lata-mas/DH2O/Imagenes/BaseCarcasa.PNG

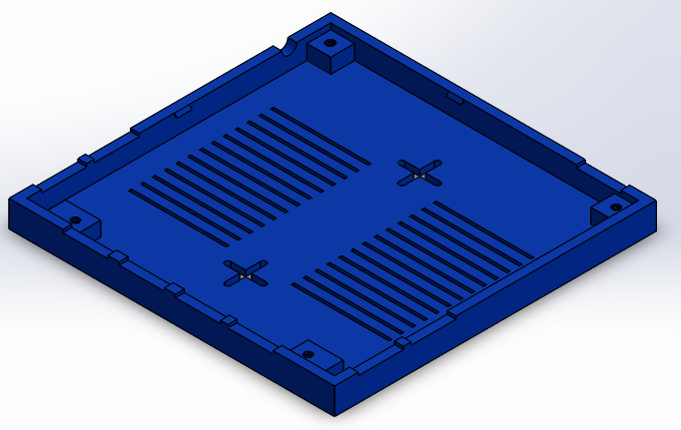
Imagenes/BaseCarcasa.PNG
