lata-mas/DH2O/Imagenes/BaseDeCarcasaPCB.PNG

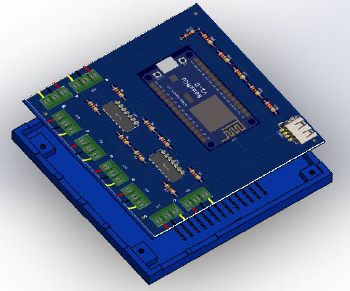
Imagenes/BaseDeCarcasaPCB.PNG
