lata-mas/DH2O/Imagenes/BaseDeCarcasaTornillos.PNG

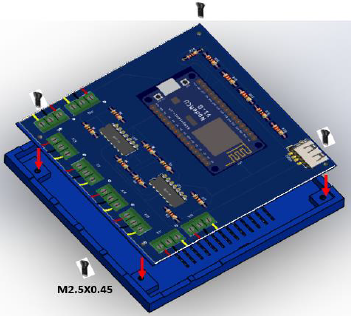
Imagenes/BaseDeCarcasaTornillos.PNG
