lata-mas/DH2O/Imagenes/BaseMediaCarcasa.PNG

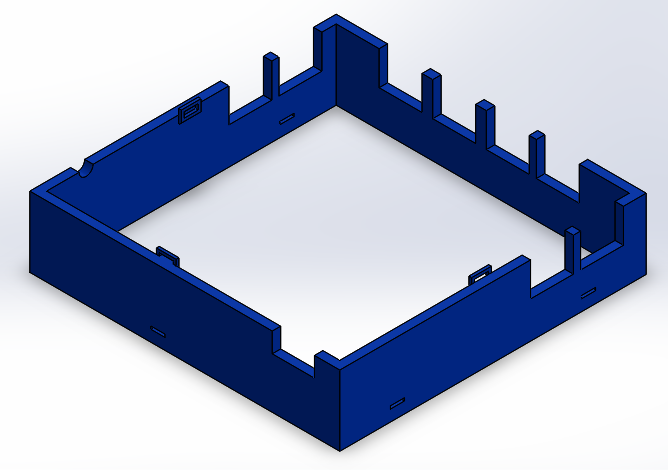
Imagenes/BaseMediaCarcasa.PNG
