lata-mas/DH2O/Imagenes/BASEYPLACA1.PNG

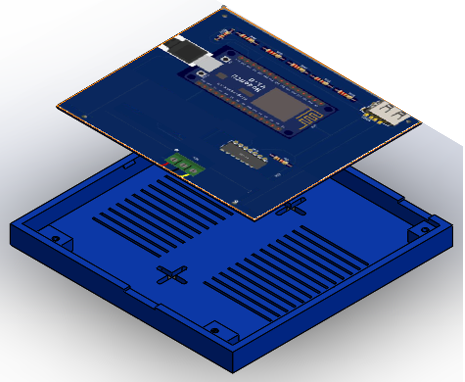
Imagenes/BASEYPLACA1.PNG
