lata-mas/DH2O/Imagenes/BASEYPLACA.PNG

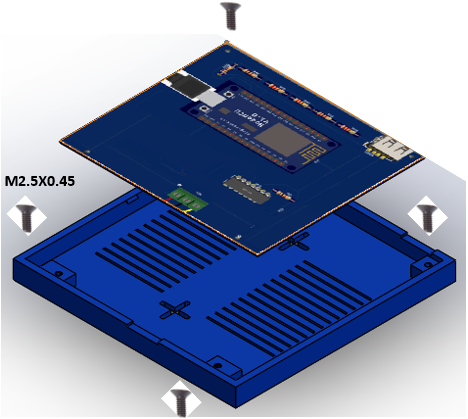
Imagenes/BASEYPLACA.PNG
