lata-mas/DH2O/Imagenes/CarateristicasNodeMCU.PNG

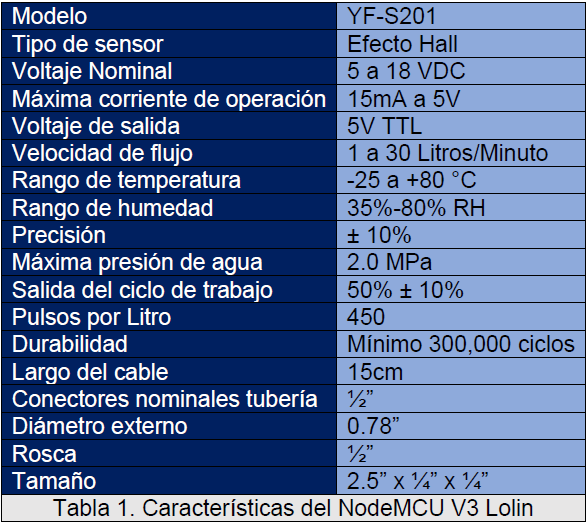
Imagenes/CarateristicasNodeMCU.PNG
