lata-mas/DH2O/Imagenes/CarateristicasNodeMCUB.PNG

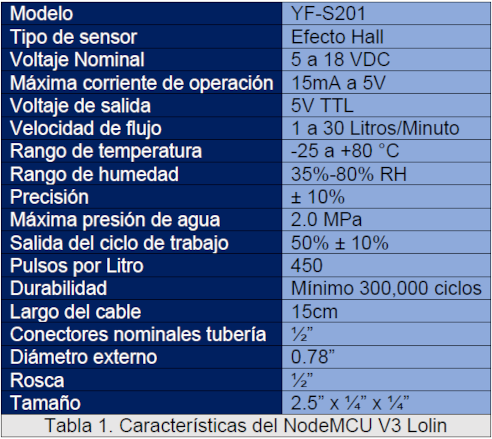
Imagenes/CarateristicasNodeMCUB.PNG
