lata-mas/DH2O/Imagenes/CarcasaH2O.PNG

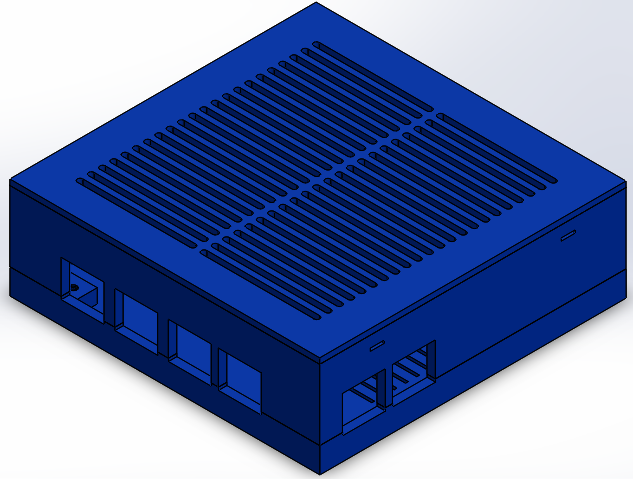
Imagenes/CarcasaH2O.PNG
