lata-mas/DH2O/Imagenes/Codigo5.PNG

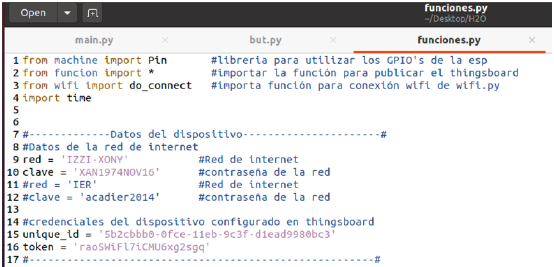
Imagenes/Codigo5.PNG
