lata-mas/DH2O/Imagenes/Codigo5B.PNG

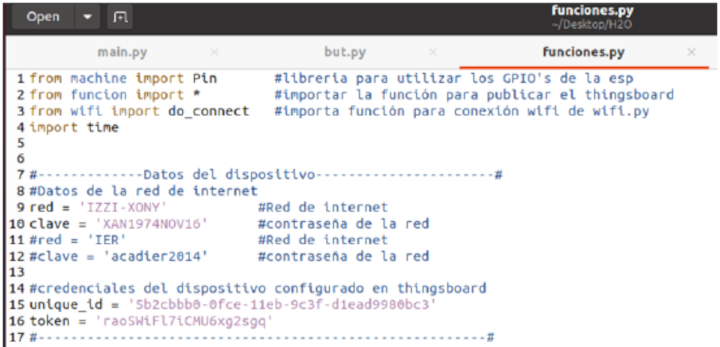
Imagenes/Codigo5B.PNG
