lata-mas/DH2O/Imagenes/COMPONENTESENPLACACOMPLETA.PNG

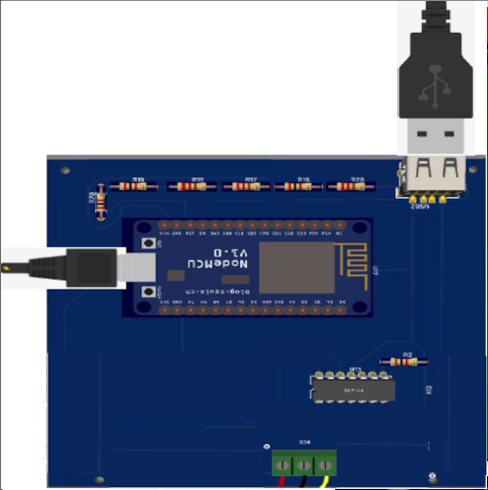
Imagenes/COMPONENTESENPLACACOMPLETA.PNG
