lata-mas/DH2O/Imagenes/Conexión de 2 sensores H2O.PNG

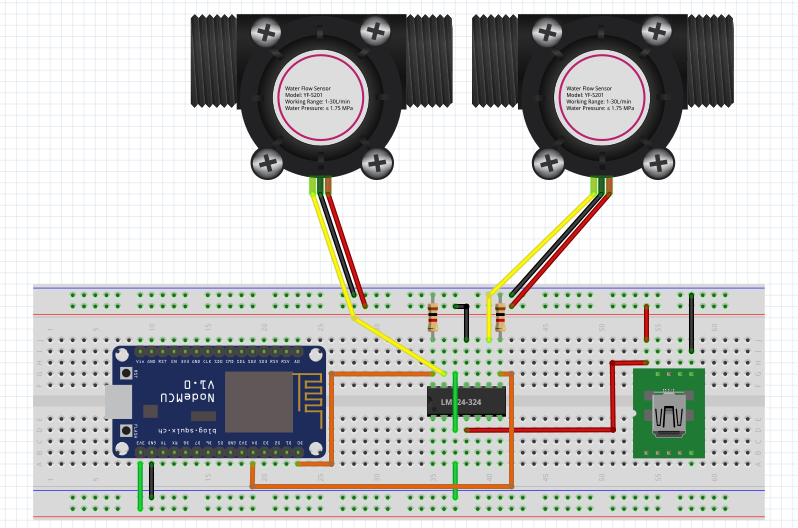
Imagenes/Conexión de 2 sensores H2O.PNG
