lata-mas/DH2O/Imagenes/Conexión_1S.PNG

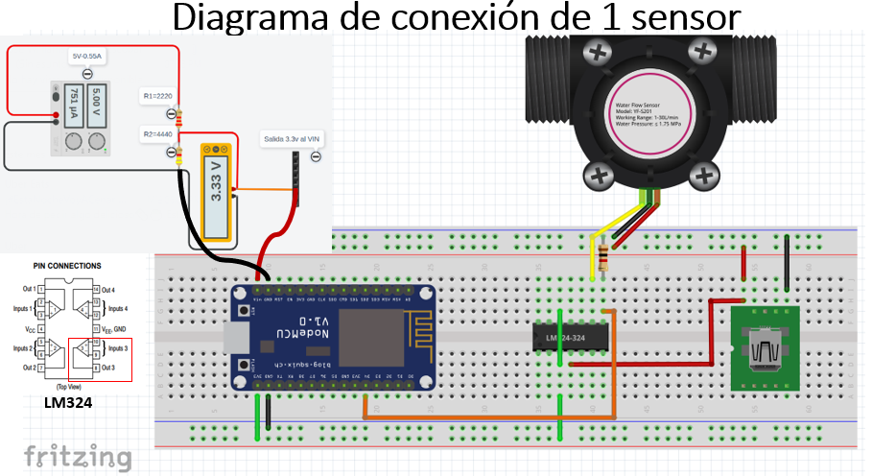
Imagenes/Conexión_1S.PNG
