lata-mas/DH2O/Imagenes/Conexión_8S H2O.PNG

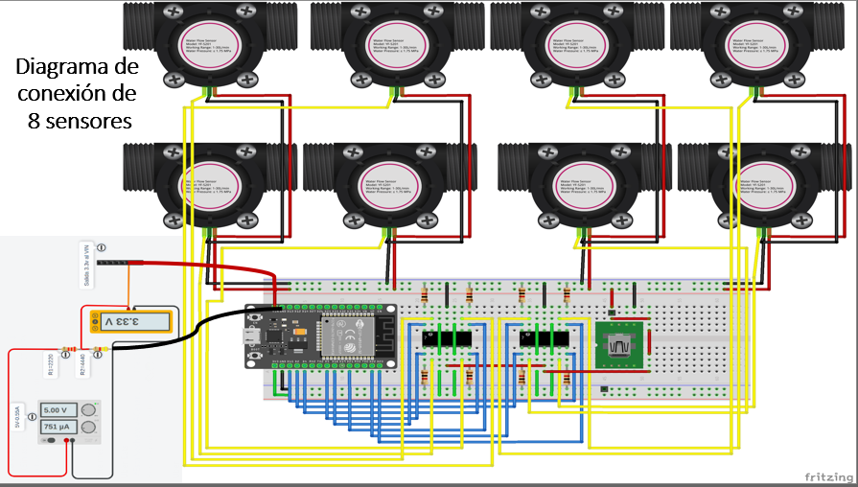
Imagenes/Conexión_8S H2O.PNG
