lata-mas/DH2O/Imagenes/CORRECTOINCORRECTO.PNG

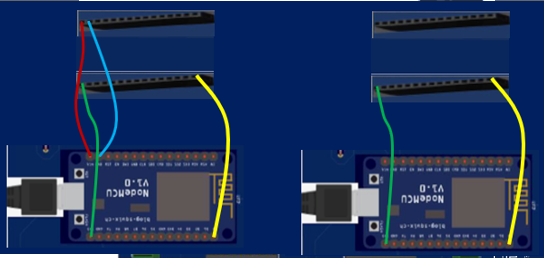
Imagenes/CORRECTOINCORRECTO.PNG
