lata-mas/DH2O/Imagenes/DetallesNodeMCU.PNG

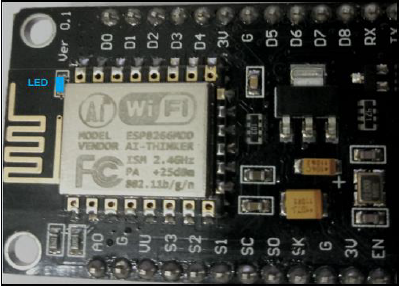
Imagenes/DetallesNodeMCU.PNG
