lata-mas/DH2O/Imagenes/DILLINGERB.png

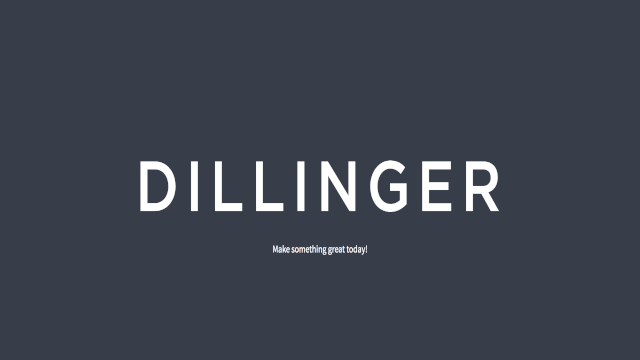
Imagenes/DILLINGERB.png
