lata-mas/DH2O/Imagenes/DimensionesPCBH2O.PNG

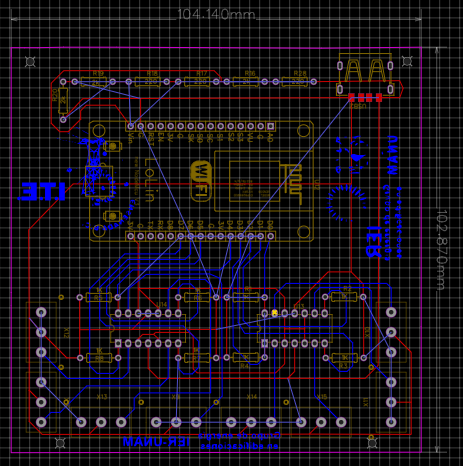
Imagenes/DimensionesPCBH2O.PNG
