lata-mas/DH2O/Imagenes/Divisor de V para el ESP-H2O.png

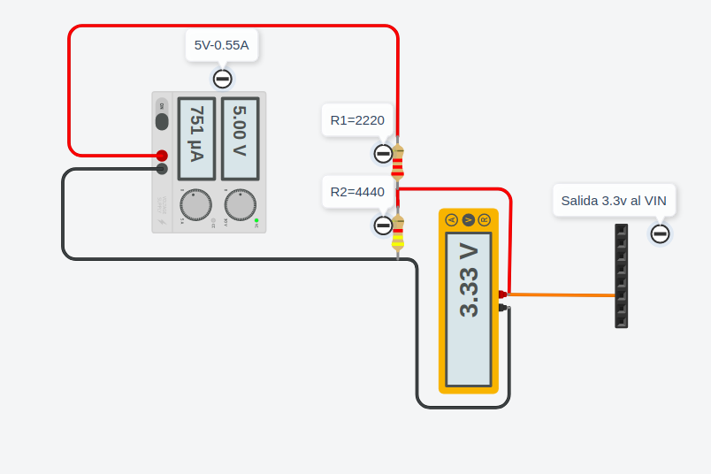
Imagenes/Divisor de V para el ESP-H2O.png
