lata-mas/DH2O/Imagenes/ErroresSolucion.PNG

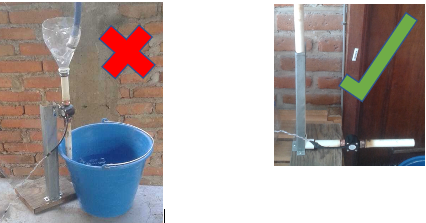
Imagenes/ErroresSolucion.PNG
