lata-mas/DH2O/Imagenes/ErroresSoluciones1.png

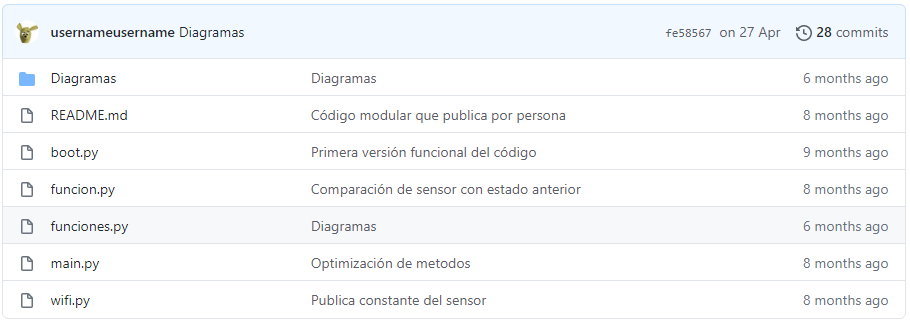
Imagenes/ErroresSoluciones1.png
