lata-mas/DH2O/Imagenes/ErroresSoluciones2.png

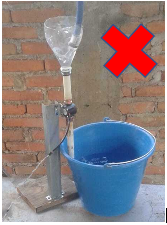
Imagenes/ErroresSoluciones2.png
