lata-mas/DH2O/Imagenes/ErroresSoluciones3.png

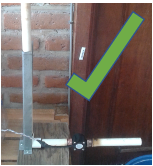
Imagenes/ErroresSoluciones3.png
