lata-mas/DH2O/Imagenes/ESPENPLACA.PNG

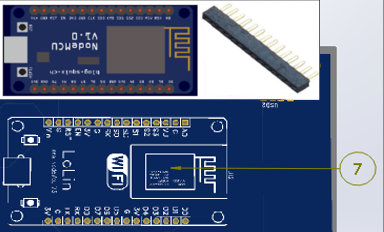
Imagenes/ESPENPLACA.PNG
