lata-mas/DH2O/Imagenes/FormaCorrectaIncorrecta.PNG

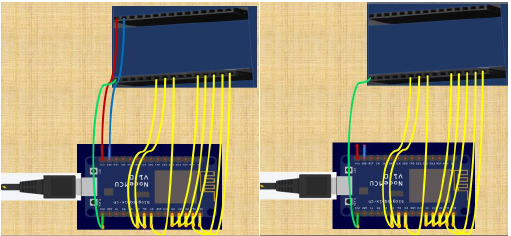
Imagenes/FormaCorrectaIncorrecta.PNG
