lata-mas/DH2O/Imagenes/IDENTIFICACIONCOMPH2O1.PNG

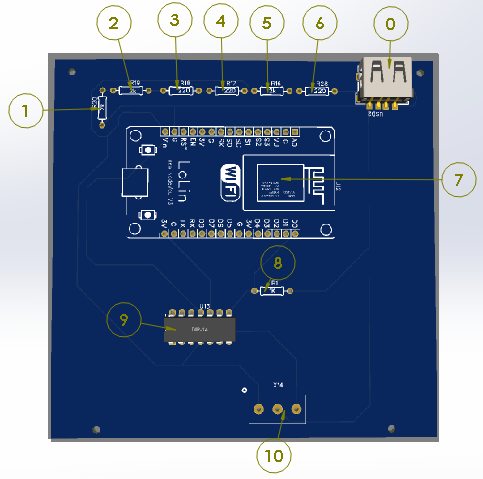
Imagenes/IDENTIFICACIONCOMPH2O1.PNG
