lata-mas/DH2O/Imagenes/IdentificacionDePatillaje.PNG

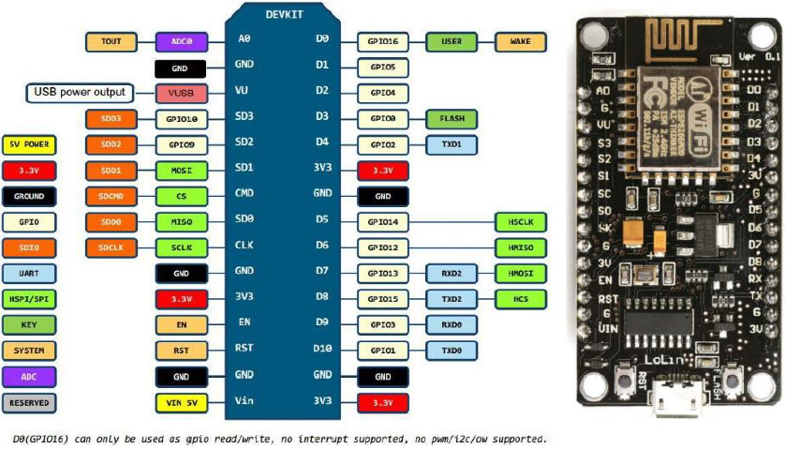
Imagenes/IdentificacionDePatillaje.PNG
