lata-mas/DH2O/Imagenes/ImagenCorteDePines.PNG

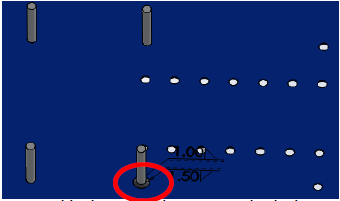
Imagenes/ImagenCorteDePines.PNG
