lata-mas/DH2O/Imagenes/ImagenESPEnPlaca.PNG

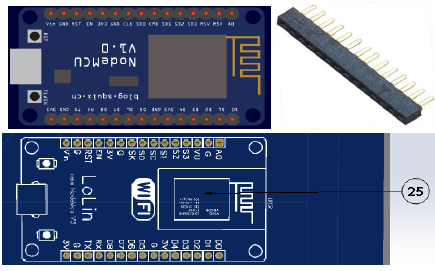
Imagenes/ImagenESPEnPlaca.PNG
