lata-mas/DH2O/Imagenes/LedESP.PNG

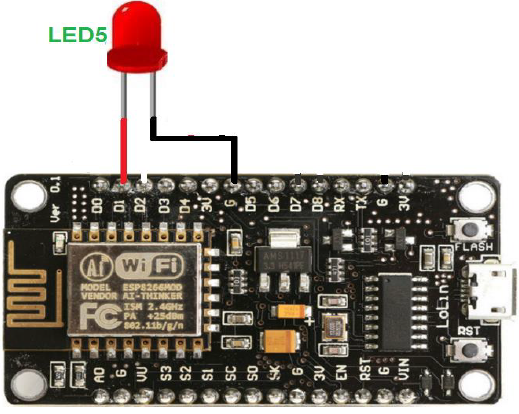
Imagenes/LedESP.PNG
