lata-mas/DH2O/Imagenes/LedsAzules.PNG

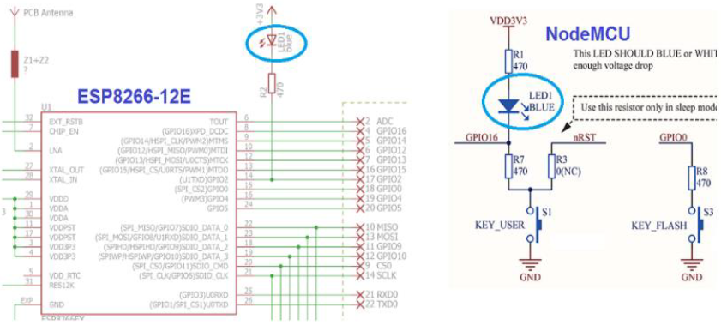
Imagenes/LedsAzules.PNG
