lata-mas/DH2O/Imagenes/ListarEnLinux.PNG

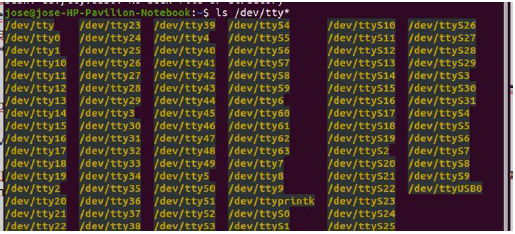
Imagenes/ListarEnLinux.PNG
