lata-mas/DH2O/Imagenes/M_Editor.PNG

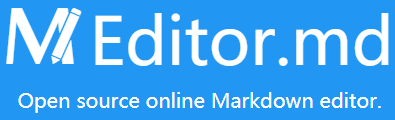
Imagenes/M_Editor.PNG
