lata-mas/DH2O/Imagenes/OpenKnow-How.PNG

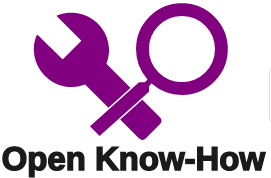
Imagenes/OpenKnow-How.PNG
