lata-mas/DH2O/Imagenes/OrientacionLM324.PNG

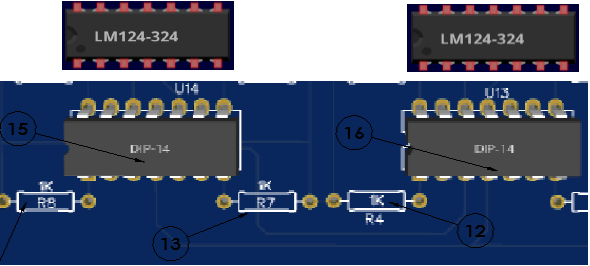
Imagenes/OrientacionLM324.PNG
