lata-mas/DH2O/Imagenes/Partes EsambleCompleto.PNG

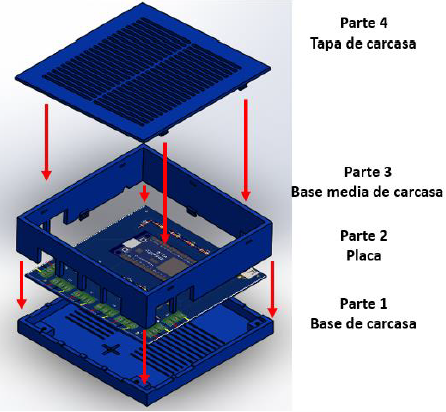
Imagenes/Partes EsambleCompleto.PNG
