lata-mas/DH2O/Imagenes/PatillajeESP.PNG

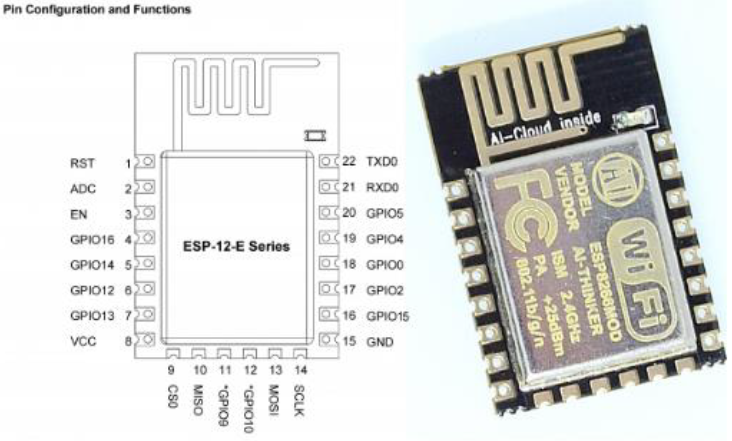
Imagenes/PatillajeESP.PNG
