lata-mas/DH2O/Imagenes/PCB3DEASYH2O1FRONTAL.PNG

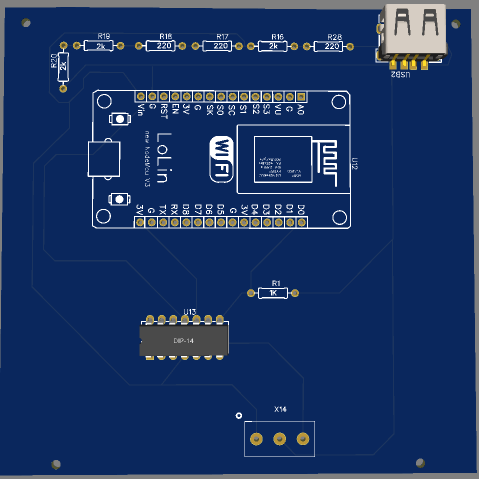
Imagenes/PCB3DEASYH2O1FRONTAL.PNG
