lata-mas/DH2O/Imagenes/PCB_H2O PCB.png

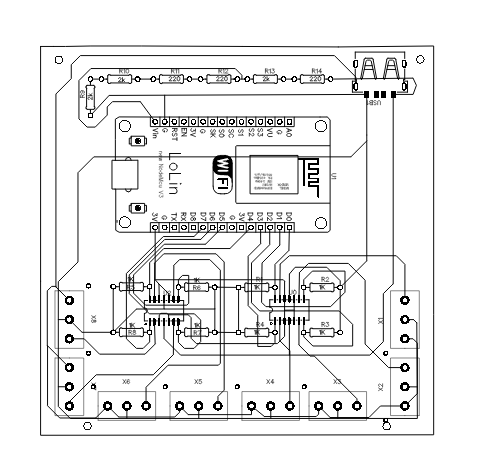
Imagenes/PCB_H2O PCB.png
