lata-mas/DH2O/Imagenes/PCBEASYH2O13DABAJO.PNG

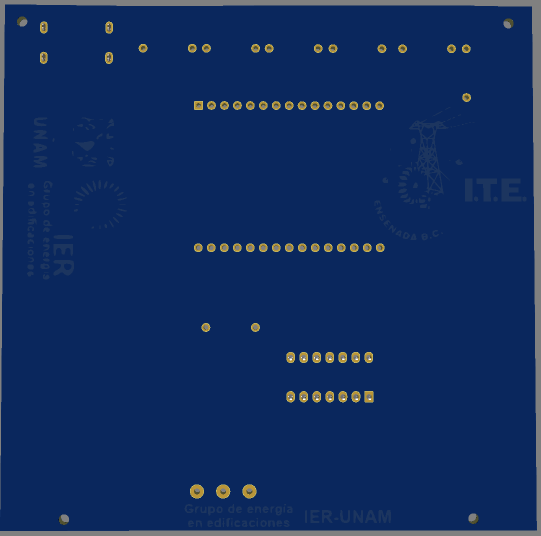
Imagenes/PCBEASYH2O13DABAJO.PNG
