lata-mas/DH2O/Imagenes/PinesCortados.PNG

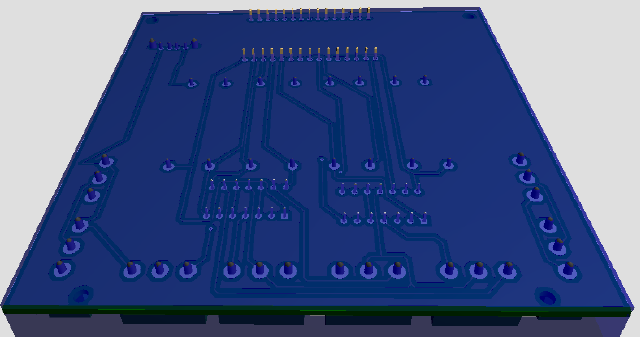
Imagenes/PinesCortados.PNG
