lata-mas/DH2O/Imagenes/PinesCortadosB.PNG

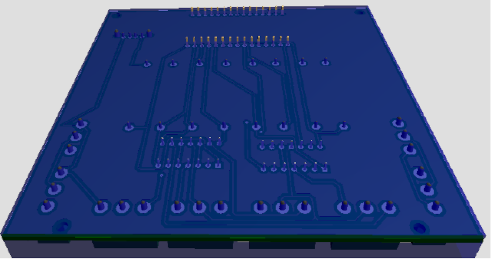
Imagenes/PinesCortadosB.PNG
