lata-mas/DH2O/Imagenes/PINESCUTPLACA1.PNG

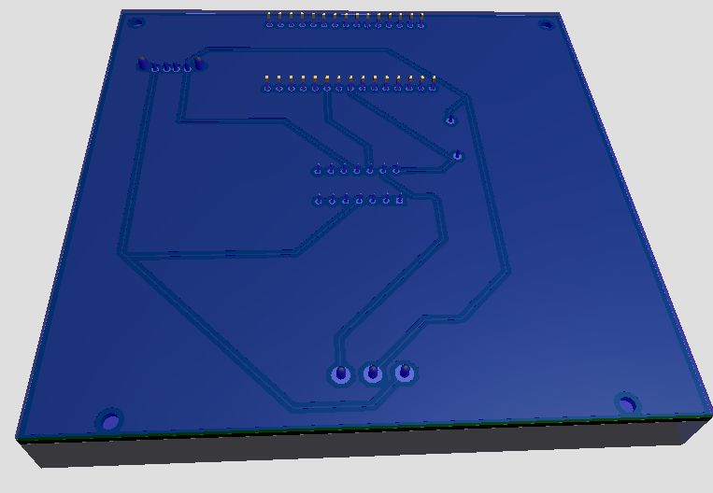
Imagenes/PINESCUTPLACA1.PNG
