lata-mas/DH2O/Imagenes/PINESCUTPLACA.PNG

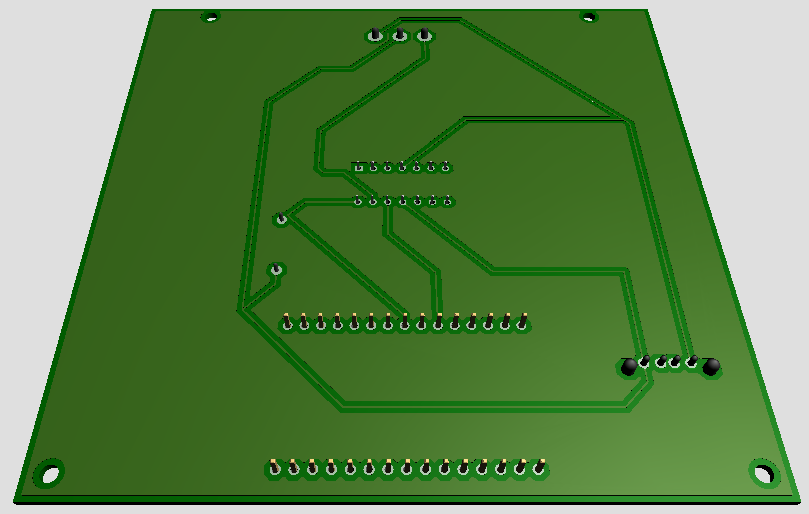
Imagenes/PINESCUTPLACA.PNG
