lata-mas/DH2O/Imagenes/PlacaWithComponetes.PNG

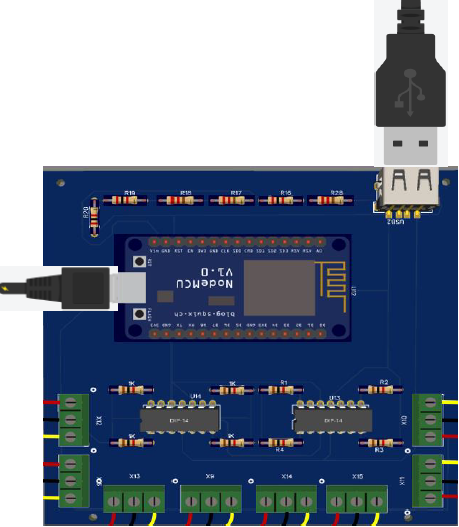
Imagenes/PlacaWithComponetes.PNG
