lata-mas/DH2O/Imagenes/PORTADAH2O1.PNG

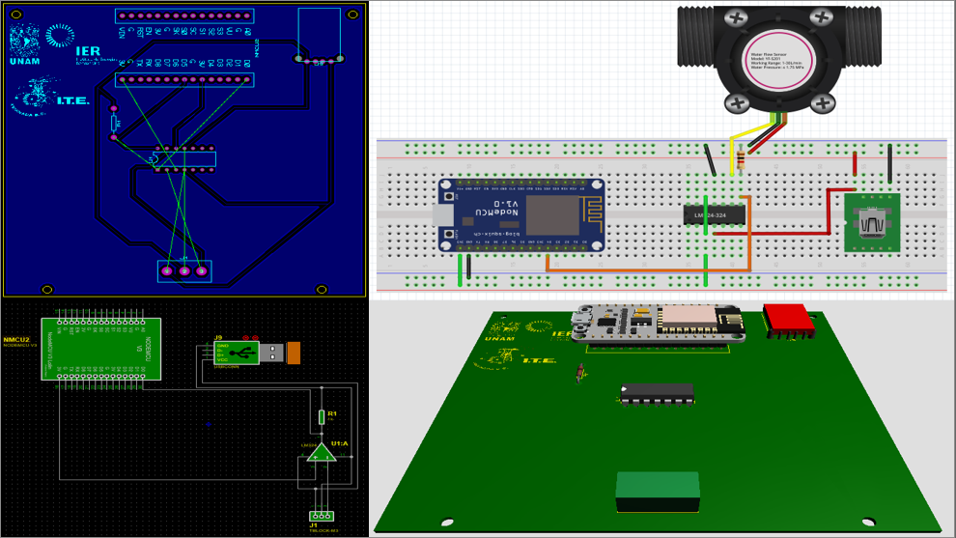
Imagenes/PORTADAH2O1.PNG
