lata-mas/DH2O/Imagenes/RelacionDeTerminales.PNG

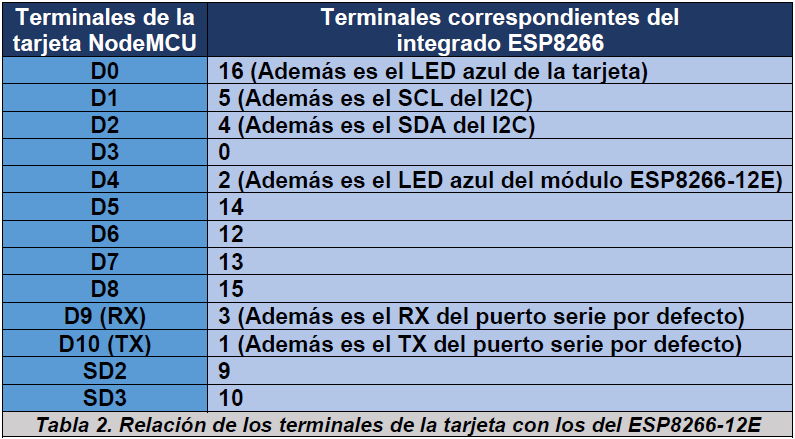
Imagenes/RelacionDeTerminales.PNG
