lata-mas/DH2O/Imagenes/ResistenciasDeParteSuperior.PNG

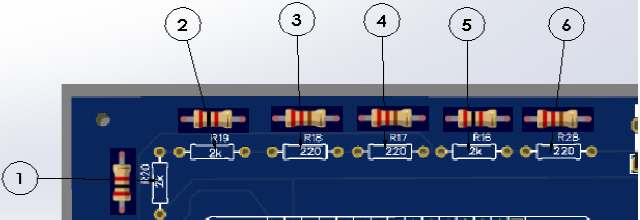
Imagenes/ResistenciasDeParteSuperior.PNG
