lata-mas/DH2O/Imagenes/ResistenciasDeParteSuperiorB.PNG

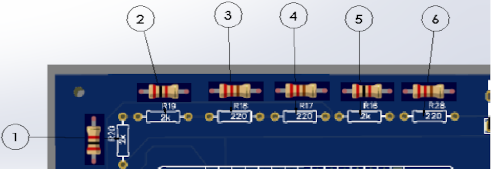
Imagenes/ResistenciasDeParteSuperiorB.PNG
