lata-mas/DH2O/Imagenes/ResistenciasParteInferior.PNG

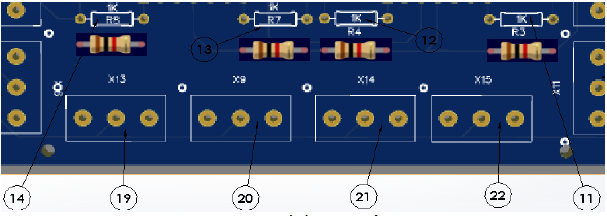
Imagenes/ResistenciasParteInferior.PNG
