lata-mas/DH2O/Imagenes/SENSORCONECTADO.PNG

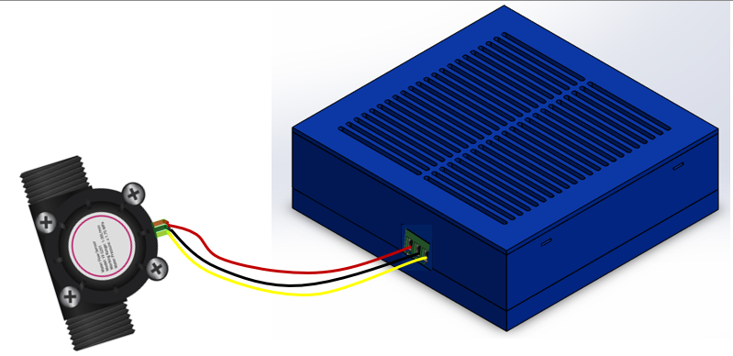
Imagenes/SENSORCONECTADO.PNG
