lata-mas/DH2O/Imagenes/SENSORENPLACA.PNG

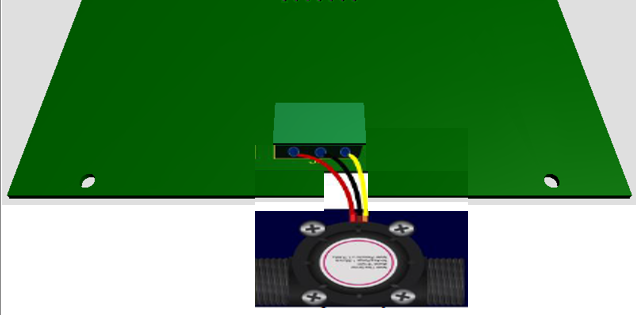
Imagenes/SENSORENPLACA.PNG
