lata-mas/DH2O/Imagenes/SensoresDerechos.PNG

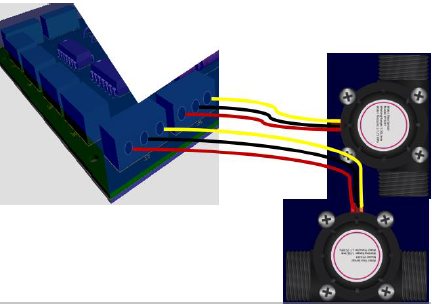
Imagenes/SensoresDerechos.PNG
