lata-mas/DH2O/Imagenes/SensoresFrontales.PNG

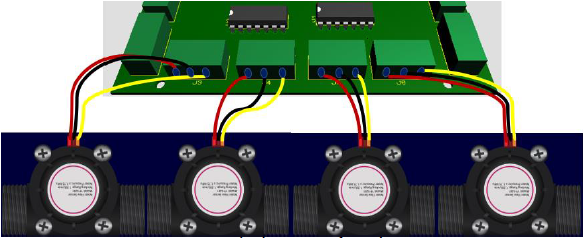
Imagenes/SensoresFrontales.PNG
