lata-mas/DH2O/Imagenes/SensoresIzquierdos.PNG

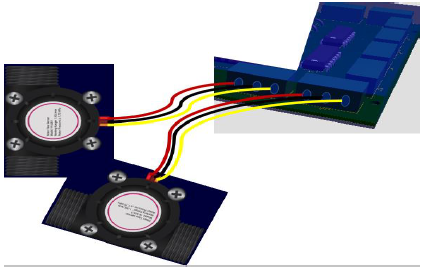
Imagenes/SensoresIzquierdos.PNG
