lata-mas/DH2O/Imagenes/TapaCarcasa.PNG

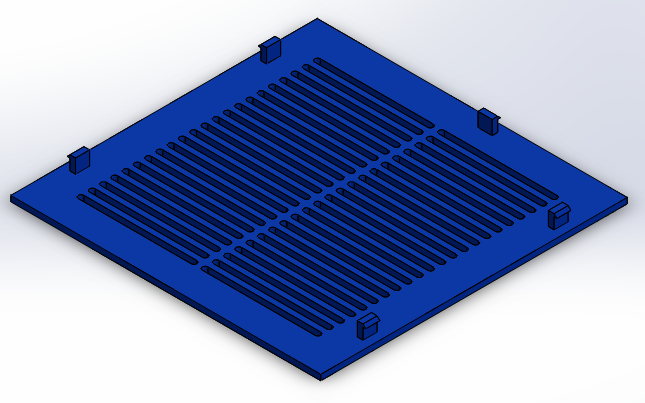
Imagenes/TapaCarcasa.PNG
