lata-mas/DH2O/Imagenes/TBLOCK-M3.PNG

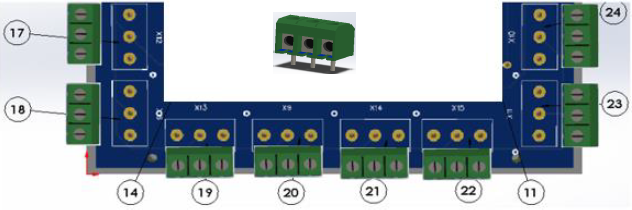
Imagenes/TBLOCK-M3.PNG
