lata-mas/DH2O/Imagenes/TBLOCKENPLACA.PNG

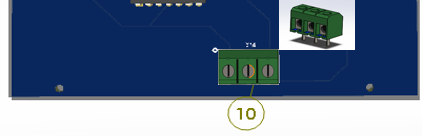
Imagenes/TBLOCKENPLACA.PNG
