lata-mas/DH2O/Imagenes/Thingsboard1.PNG

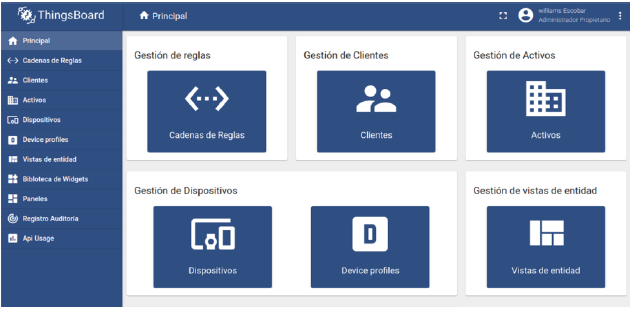
Imagenes/Thingsboard1.PNG
