lata-mas/DH2O/Imagenes/Thingsboard3.PNG

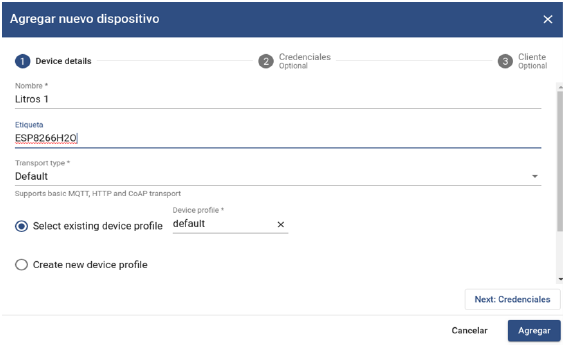
Imagenes/Thingsboard3.PNG
