lata-mas/DH2O/Imagenes/Thingsboard4.PNG

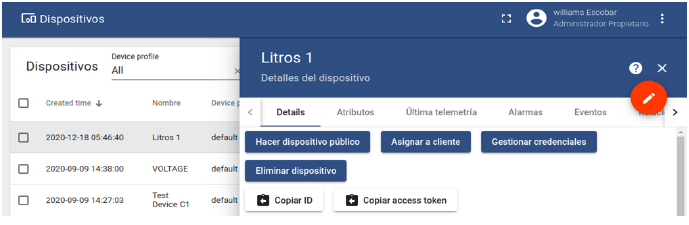
Imagenes/Thingsboard4.PNG
