lata-mas/DH2O/Imagenes/Thingsboard6.PNG

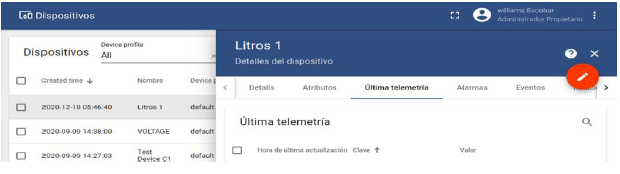
Imagenes/Thingsboard6.PNG
