lata-mas/DH2O/Imagenes/Thingsboard6B.PNG

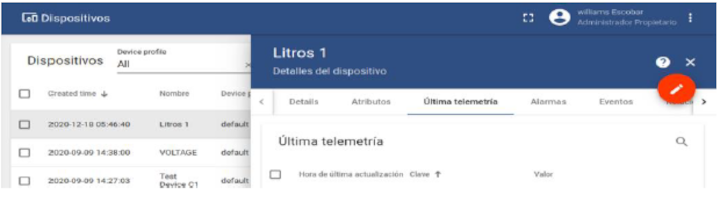
Imagenes/Thingsboard6B.PNG
