lata-mas/DH2O/Imagenes/USBCONN.PNG

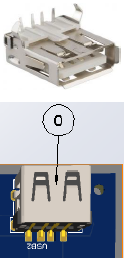
Imagenes/USBCONN.PNG
