lata-mas/DH2O/Imagenes/VersionesESP.PNG

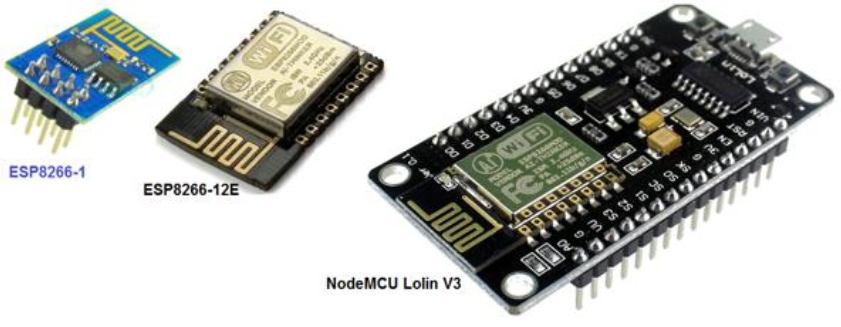
Imagenes/VersionesESP.PNG
