lata-mas/DH2O/Imagenes/VinferiorH2OPCB.PNG

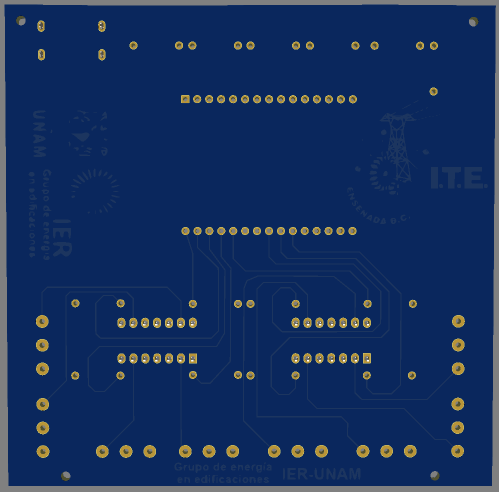
Imagenes/VinferiorH2OPCB.PNG
