lata-mas/DH2O/Imagenes/vistasuperiorpcb.PNG

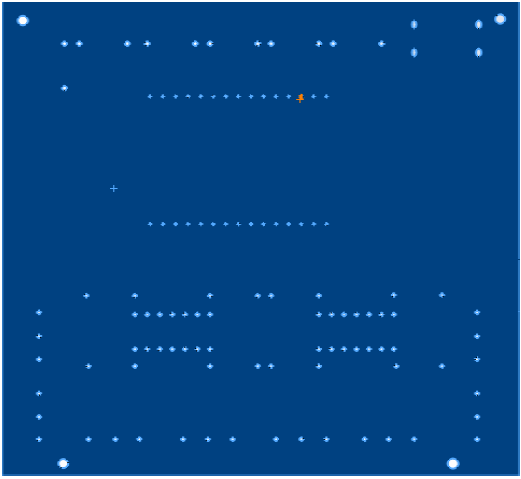
Imagenes/vistasuperiorpcb.PNG
