lata-mas/DH2O/Imagenes/VisualizacionCodigos.PNG

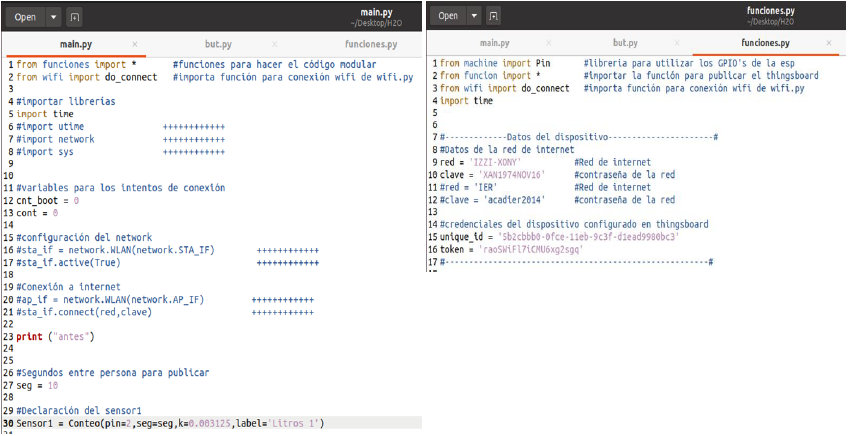
Imagenes/VisualizacionCodigos.PNG
