lata-mas/DH2O/Imagenes/VsuperiorPCBH2O.PNG

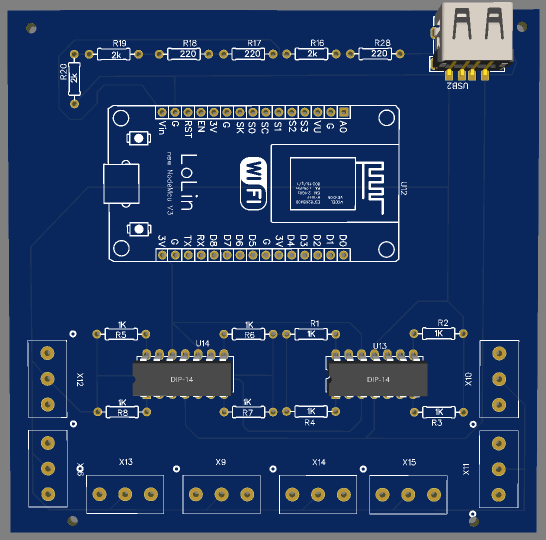
Imagenes/VsuperiorPCBH2O.PNG
