lata-mas/DH2O/Imagenes/ComponentesEnPCB.PNG

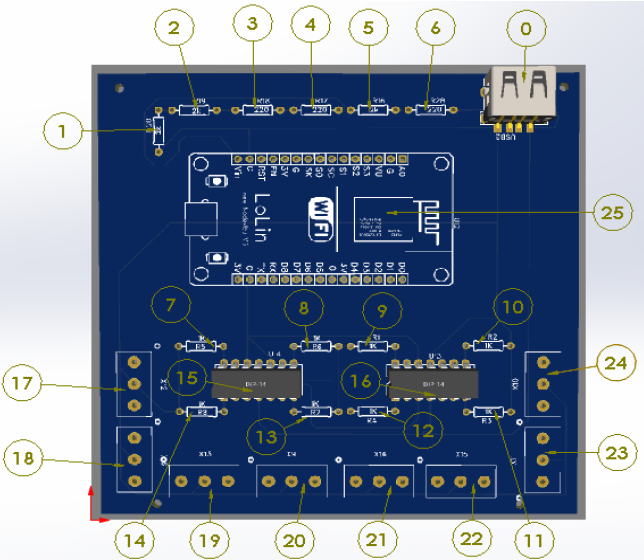
Imagenes/ComponentesEnPCB.PNG
