lata-mas/DH2O/Imagenes/globoscomponentes.PNG

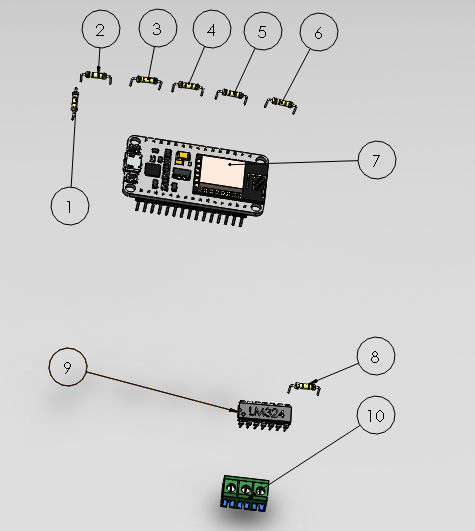
Imagenes/globoscomponentes.PNG
