lata-mas/DH2O/Imagenes/IdentificacionDeComponentes.PNG

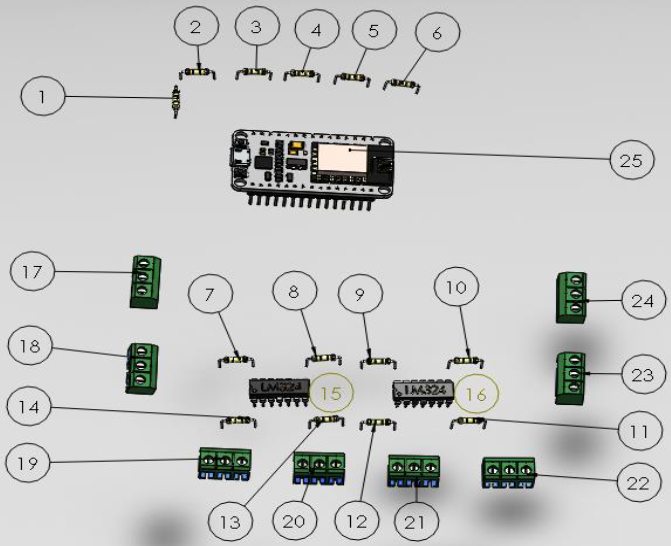
Imagenes/IdentificacionDeComponentes.PNG
