lata-mas/DH2O/Imagenes/TABLACOMPONENTES.PNG

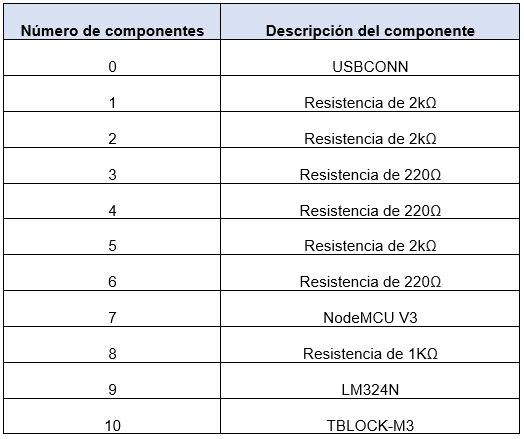
Imagenes/TABLACOMPONENTES.PNG
