lata-mas/DH2O/Imagenes/TablaDeComponentes.PNG

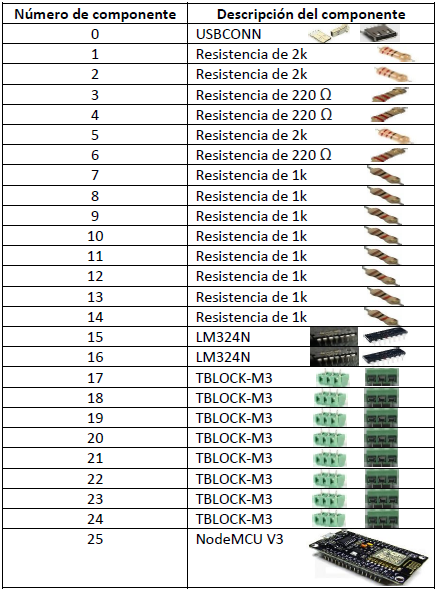
Imagenes/TablaDeComponentes.PNG
