lata-mas/DH2O/Imagenes/TablaDeComponentesB.PNG

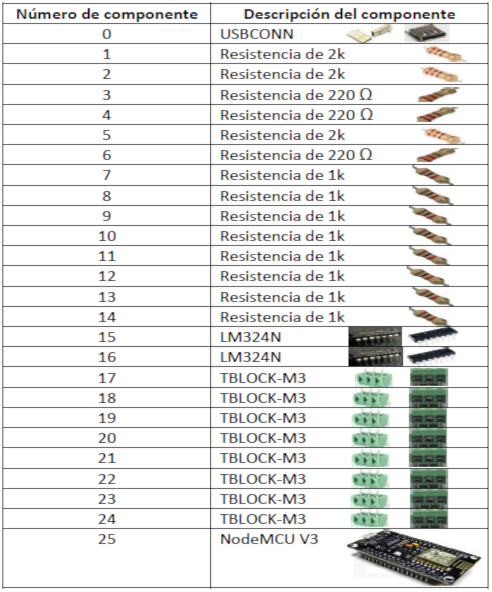
Imagenes/TablaDeComponentesB.PNG
