lata-mas/DH2O/Imagenes/ENSAMBLEFINAL.PNG

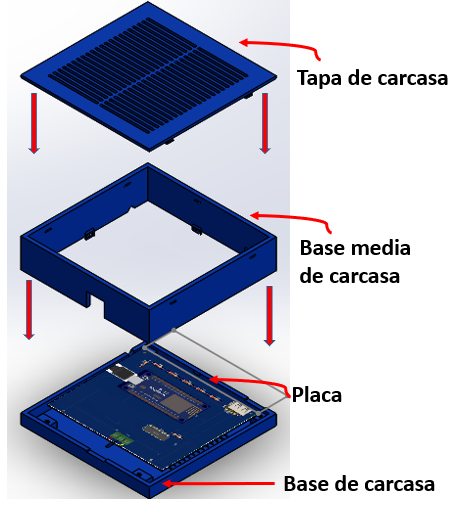
Imagenes/ENSAMBLEFINAL.PNG
