lata-mas/DH2O/Imagenes/MontajeParaPrueba.PNG

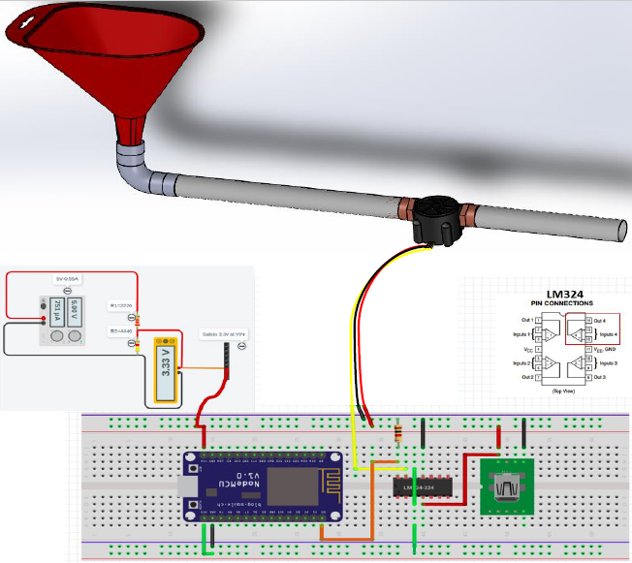
Imagenes/MontajeParaPrueba.PNG
