lata-mas/DH2O/Imagenes/OManualB.PNG

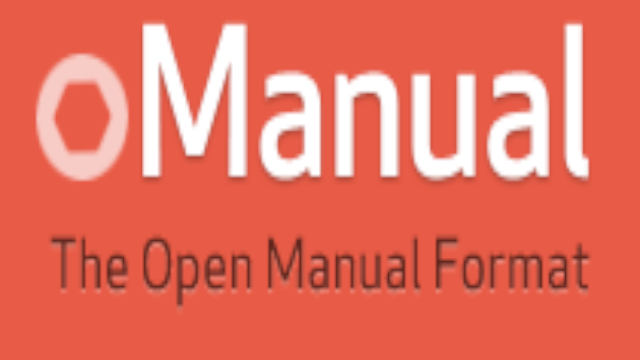
Imagenes/OManualB.PNG
