lata-mas/DH2O/Imagenes/VistaEnsambleCompleto.PNG

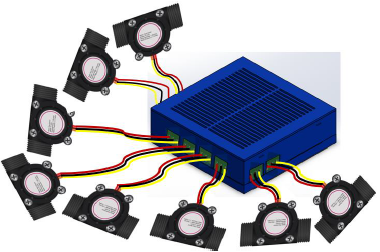
Imagenes/VistaEnsambleCompleto.PNG
