lata-mas/DH2O/Imagenes/CalibrarSensor1.PNG

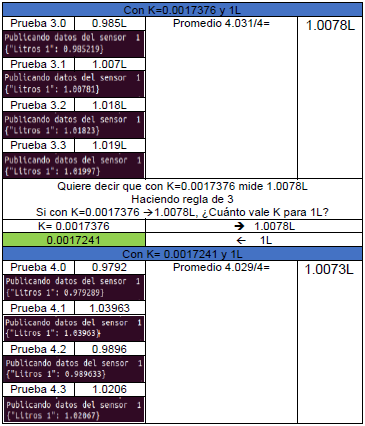
Imagenes/CalibrarSensor1.PNG
