lata-mas/DH2O/Imagenes/CalibrarSensor.PNG

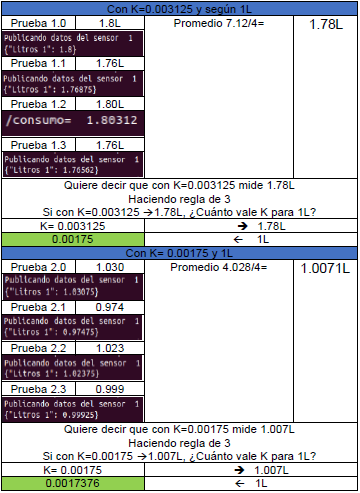
Imagenes/CalibrarSensor.PNG
