lata-mas/DH2O/Imagenes/PruebaDeEncendido.PNG

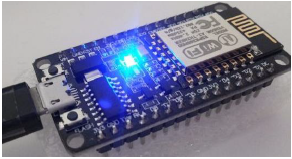
Imagenes/PruebaDeEncendido.PNG
