lata-mas/DH2O/Imagenes/PruebaMpfshell.PNG

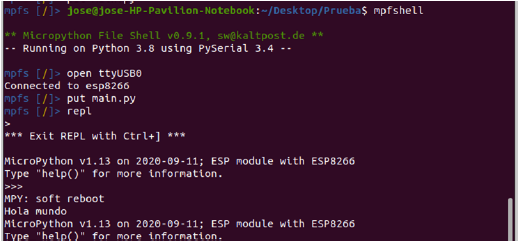
Imagenes/PruebaMpfshell.PNG
